devdrik/robo-arm/code/pi/robocli.py

import time

class RoboCLI():

    def __init__(self, actionHandler, robo):
        self.actionHandler = actionHandler
        self.robo = robo
    
    def startTeachingCli(self):
        while True:
            self.robo.startTeachMode()
            menu = self.__getMenu()
            inp = input(menu)
            try:
                if inp == 'q':
                    break
                inp = int(inp)
            except:
                continue
            if inp == 1:
                self.__setPosition()
            elif inp == 2:
                self.__saveToFile()
            elif inp == 3:
                self.__apendFromFile()
            elif inp == 4:
                self.__runActions()
            elif inp == 5:
                self.actionHandler.clearActions()
            elif inp == 6:
                self.__setVelocity()
            elif inp == 7:
                self.__addPause()
            elif inp == 8:
                self.__deleteLastEntry()
            elif inp == 9:
                self.__showEntries()

    def __setPosition(self):
        self.actionHandler.setPosition()

    def __saveToFile(self):
        fname = input("enter filename: ")
        self.actionHandler.saveToFile(fname)

    def __apendFromFile(self):
        fname = input("enter filename: ")
        self.actionHandler.appendFromFile(fname)

    def __runActions(self):
        self.actionHandler.runActions(self.__getVelocityInput())

    def __setVelocity(self):
        self.actionHandler.setVelocity(self.__getVelocityInput())

    def __addPause(self):
        self.actionHandler.addPause(self.__getFloatInput("enter pause in [s]: "))


    def __getMenu(self):
        menu = ""
        for option in self.__getOptions():
            menu += option + '\n'
        menu += "your choice: "
        return menu

    def __getOptions(self):
        options=[
            "[1] set Position",
            "[2] save to file",
            "[3] read from file (append)",
            "[4] run actions",
            "[5] clear angles",
            "[6] change velocity",
            "[7] add pause",
            "[8] remove last entry",
            "[9] show entries",
            "[q] end"
        ]
        return options

    def __getVelocityInput(self):
        while True:
            vel = input("enter velocity: ")
            try:
                vel = int(vel)
            except:
                print("Not a number, try again")
                continue
            break
        return vel

    def __getFloatInput(self, request="enter float value: "):
        while True:
            val = input(request)
            try:
                val = float(val)
            except:
                print("Not a number, try again")
                continue
            break
        return val

    def __deleteLastEntry(self):
        self.actionHandler.deleteLastEntry()
    
    def __showEntries(self):
        self.actionHandler.showEntries()
