devdrik/robo-arm/code/pi/imageprocessor.py

from imutils.video import VideoStream
import numpy as np
import cv2
import imutils
import time
import myutils
from myLogger import log

class ImageProcessor():

    def __init__(self):
        self.position = (10,10)
        # self.lowerColor = (0, 80, 138)
        # self.upperColor = (38, 251, 255)
        # self.lowerColor = (9, 40, 130)
        # self.upperColor = (53, 255, 255)
        self.lowerColor = (10, 53, 202)
        self.upperColor = (58, 227, 255)
        self.contour = None

    def __del__(self):
        pass

    def getPositionFromFrame(self, frame):
        center = None
        if frame is None:
            log("no frame available", "WARN")
            return self.position
        # blur the frame, and convert it to the HSV color space
        # frame = imutils.resize(frame, width=600)
        blurred = cv2.GaussianBlur(frame, (11, 11), 0)
        hsv = cv2.cvtColor(blurred, cv2.COLOR_BGR2HSV)
        # construct a mask for the color, then perform
        # a series of dilations and erosions to remove any small
        # blobs left in the mask
        mask = cv2.inRange(hsv, self.lowerColor, self.upperColor)
        mask = cv2.erode(mask, None, iterations=2)
        mask = cv2.dilate(mask, None, iterations=2)
		# find contours in the mask
        cnts = cv2.findContours(mask.copy(), cv2.RETR_EXTERNAL,
            cv2.CHAIN_APPROX_SIMPLE)
        cnts = imutils.grab_contours(cnts)
        # only proceed if at least one contour was found
        if len(cnts) > 0:
            # log("found contour!", "OK")
            # find the largest contour in the mask
            c = max(cnts, key=cv2.contourArea)
            ((xc, yc), radius) = cv2.minEnclosingCircle(c)
            if radius > 10:
                M = cv2.moments(c)
                center = (int(M["m10"] / M["m00"]), int(M["m01"] / M["m00"]))
                x = myutils.map(center[0], 0, 600, -100, 100)
                x *= -0.7
                y = myutils.map(center[1], 50, 300, 0, 80)
                y= 80 - y
                self.position = (x, y)
                self.contour = c
        else:
            log("no contour found", "WARN")
        # log("Position is {}".format(self.position))
        return self.position
